wafer-space/chip-on-board-wire-bonded-pcbs/images/prototype1/20251208_205731.jpg

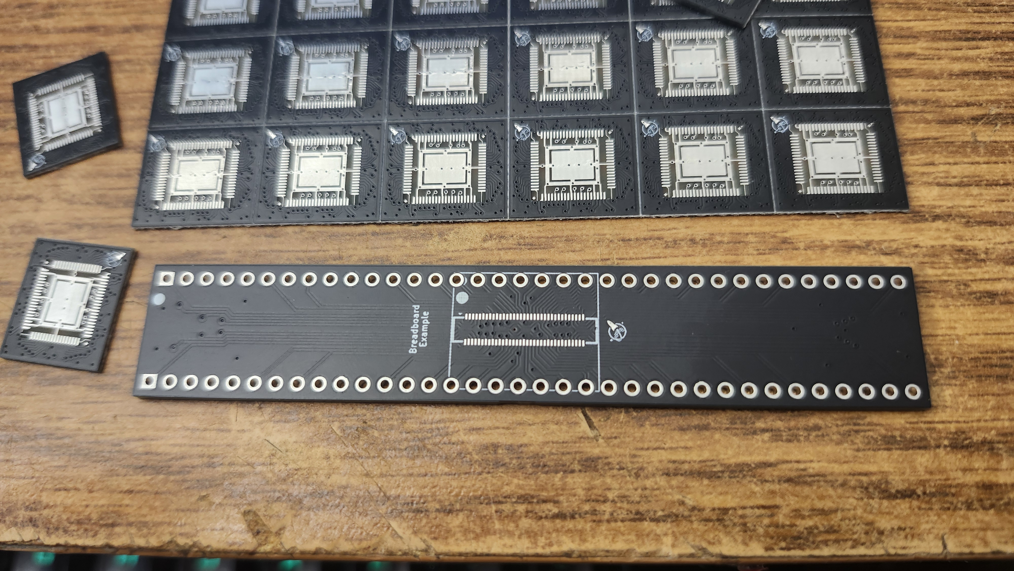
images/prototype1/20251208_205731.jpg
