wafer-space/chip-on-board-wire-bonded-pcbs/images/prototype1/20251208_205753.jpg

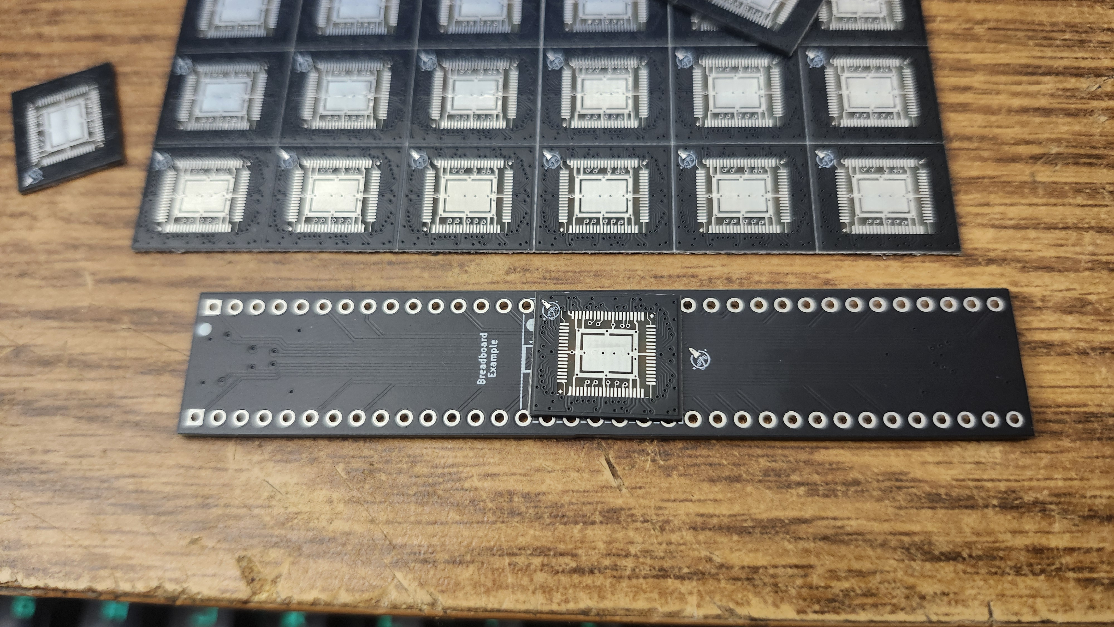
images/prototype1/20251208_205753.jpg
