wafer-space/chip-on-board-wire-bonded-pcbs/images/prototype1/20251208_210338.jpg

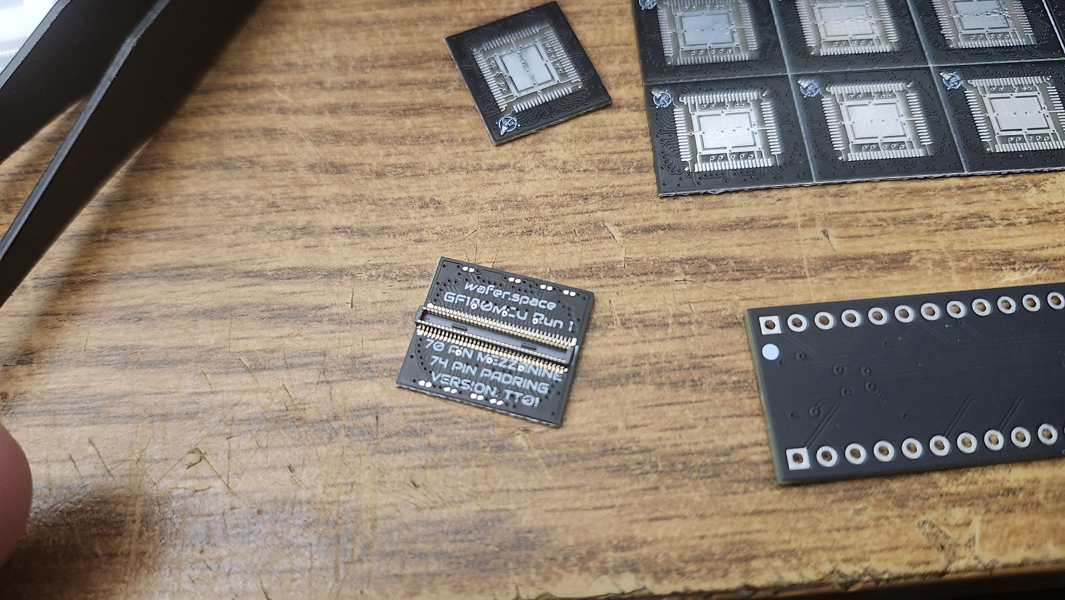
images/prototype1/20251208_210338.jpg
