wafer-space/chip-on-board-wire-bonded-pcbs/images/prototype1/20251208_210347.jpg

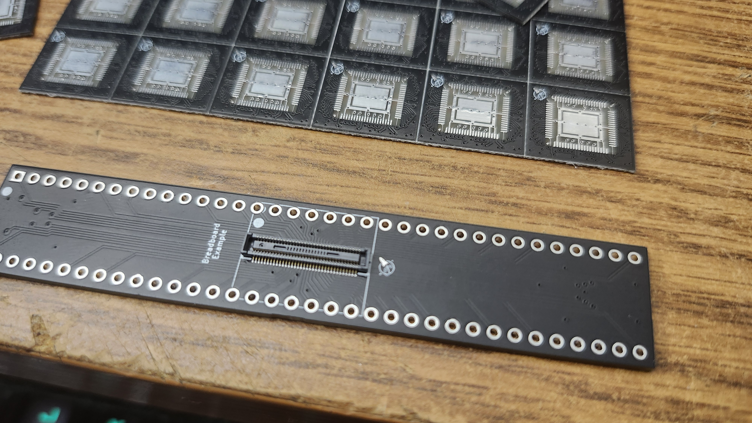
images/prototype1/20251208_210347.jpg
