wafer-space/chip-on-board-wire-bonded-pcbs/images/prototype1/20251217_000424.jpg

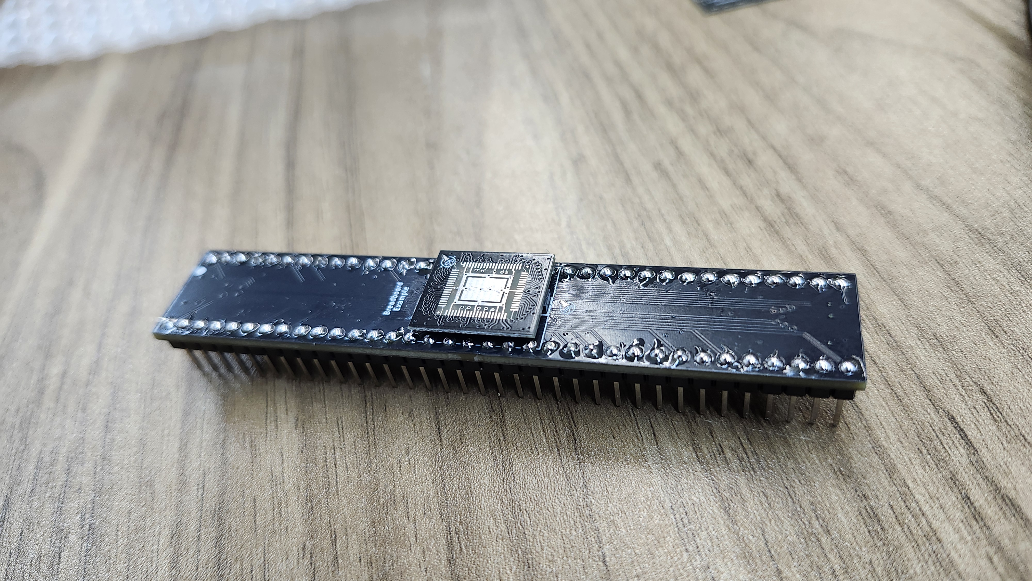
images/prototype1/20251217_000424.jpg
