wafer-space/chip-on-board-wire-bonded-pcbs/images/prototype1/20251217_001013.jpg

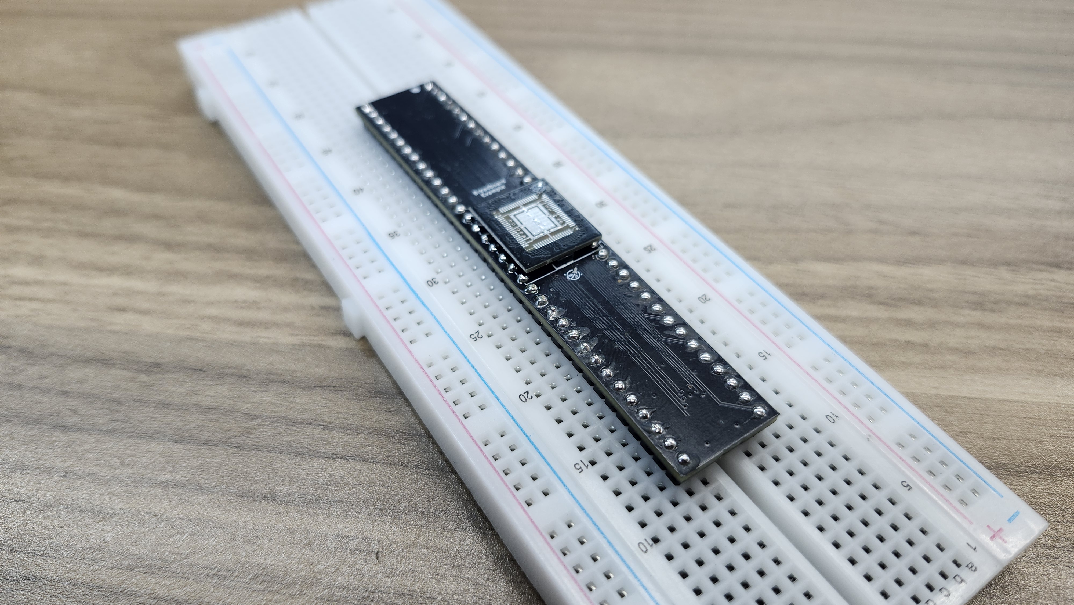
images/prototype1/20251217_001013.jpg
