wafer-space/chip-on-board-wire-bonded-pcbs/images/prototype1/20251217_001034.jpg

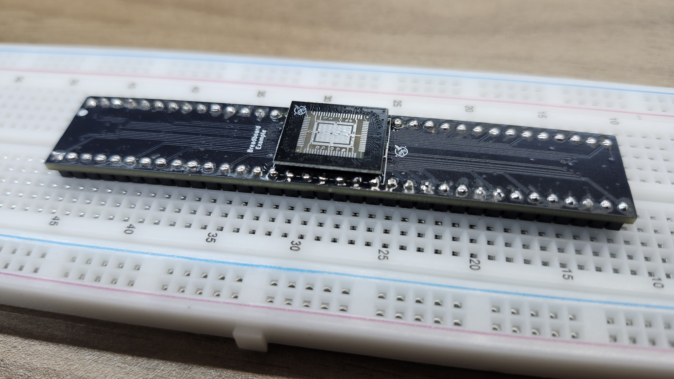
images/prototype1/20251217_001034.jpg
