wafer-space/chip-on-board-wire-bonded-pcbs/images/prototype1/20251217_003011.jpg

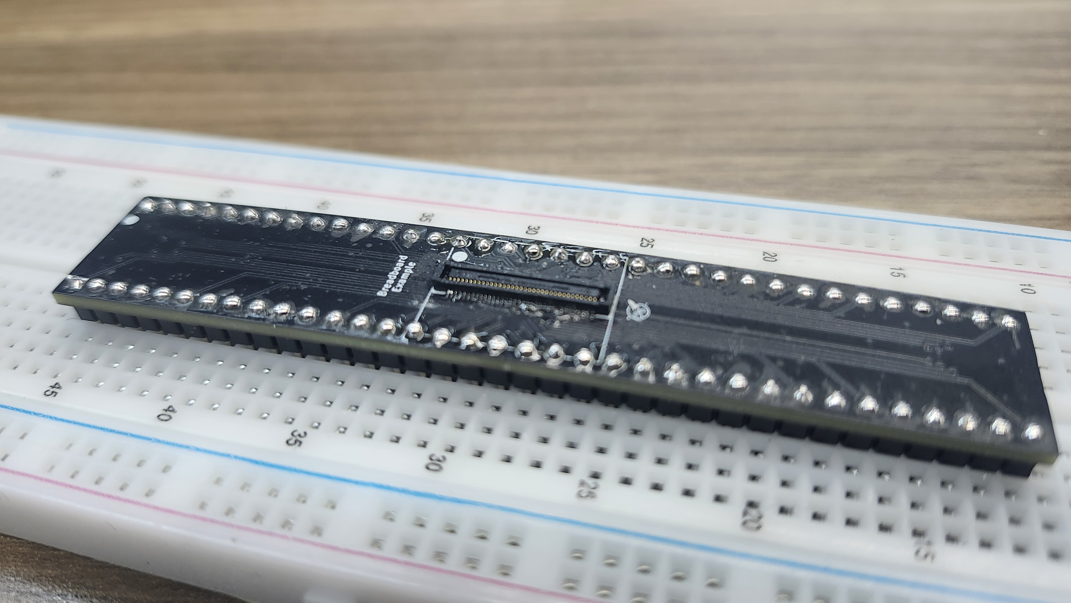
images/prototype1/20251217_003011.jpg
