wafer-space/chip-on-board-wire-bonded-pcbs/run-1/1x0p5-cob/wirebonding/ocd2.png

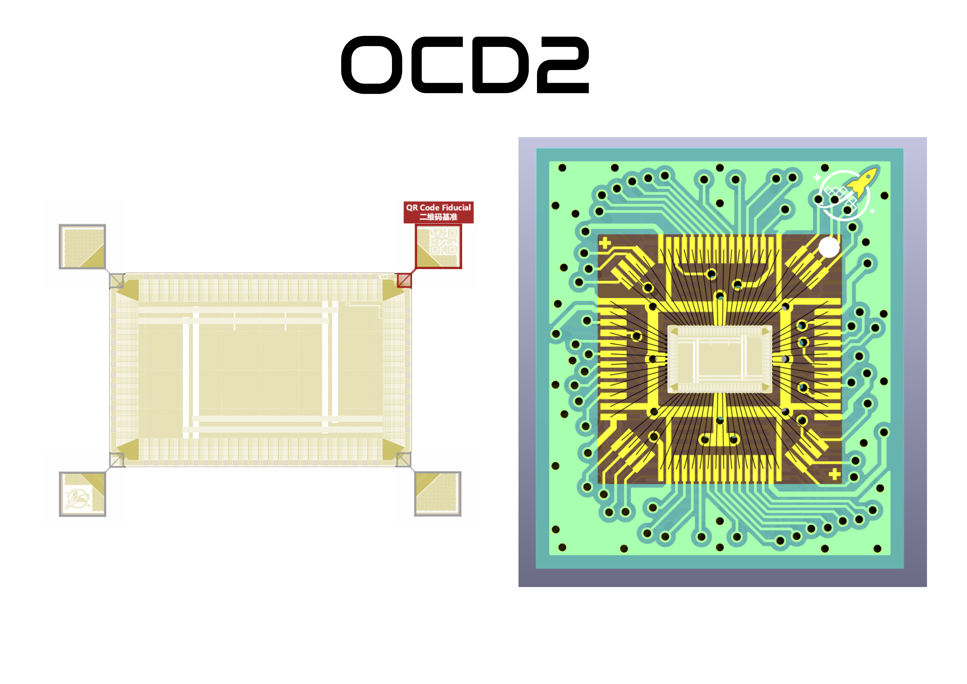
run-1/1x0p5-cob/wirebonding/ocd2.png
