wafer-space/chip-on-board-wire-bonded-pcbs/scratch/mezzanine/mezzanine/mezzanine.png

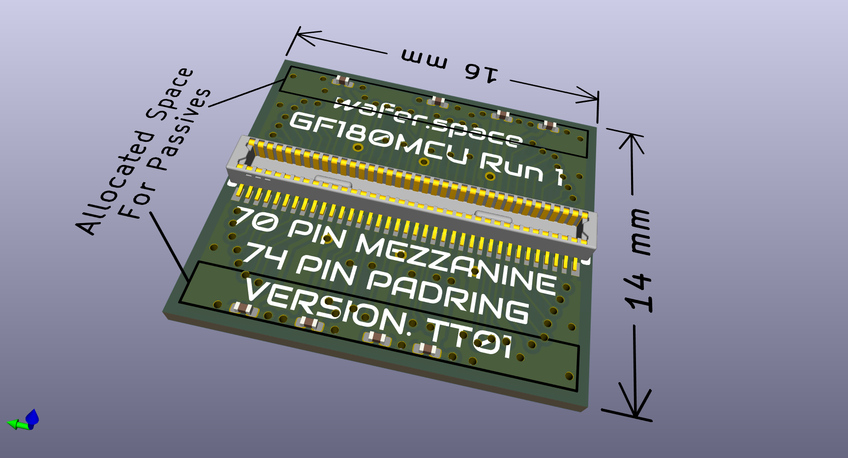
scratch/mezzanine/mezzanine/mezzanine.png
