wafer-space/chip-on-board-wire-bonded-pcbs/run-1/wirebonding/TTPG.pdf

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

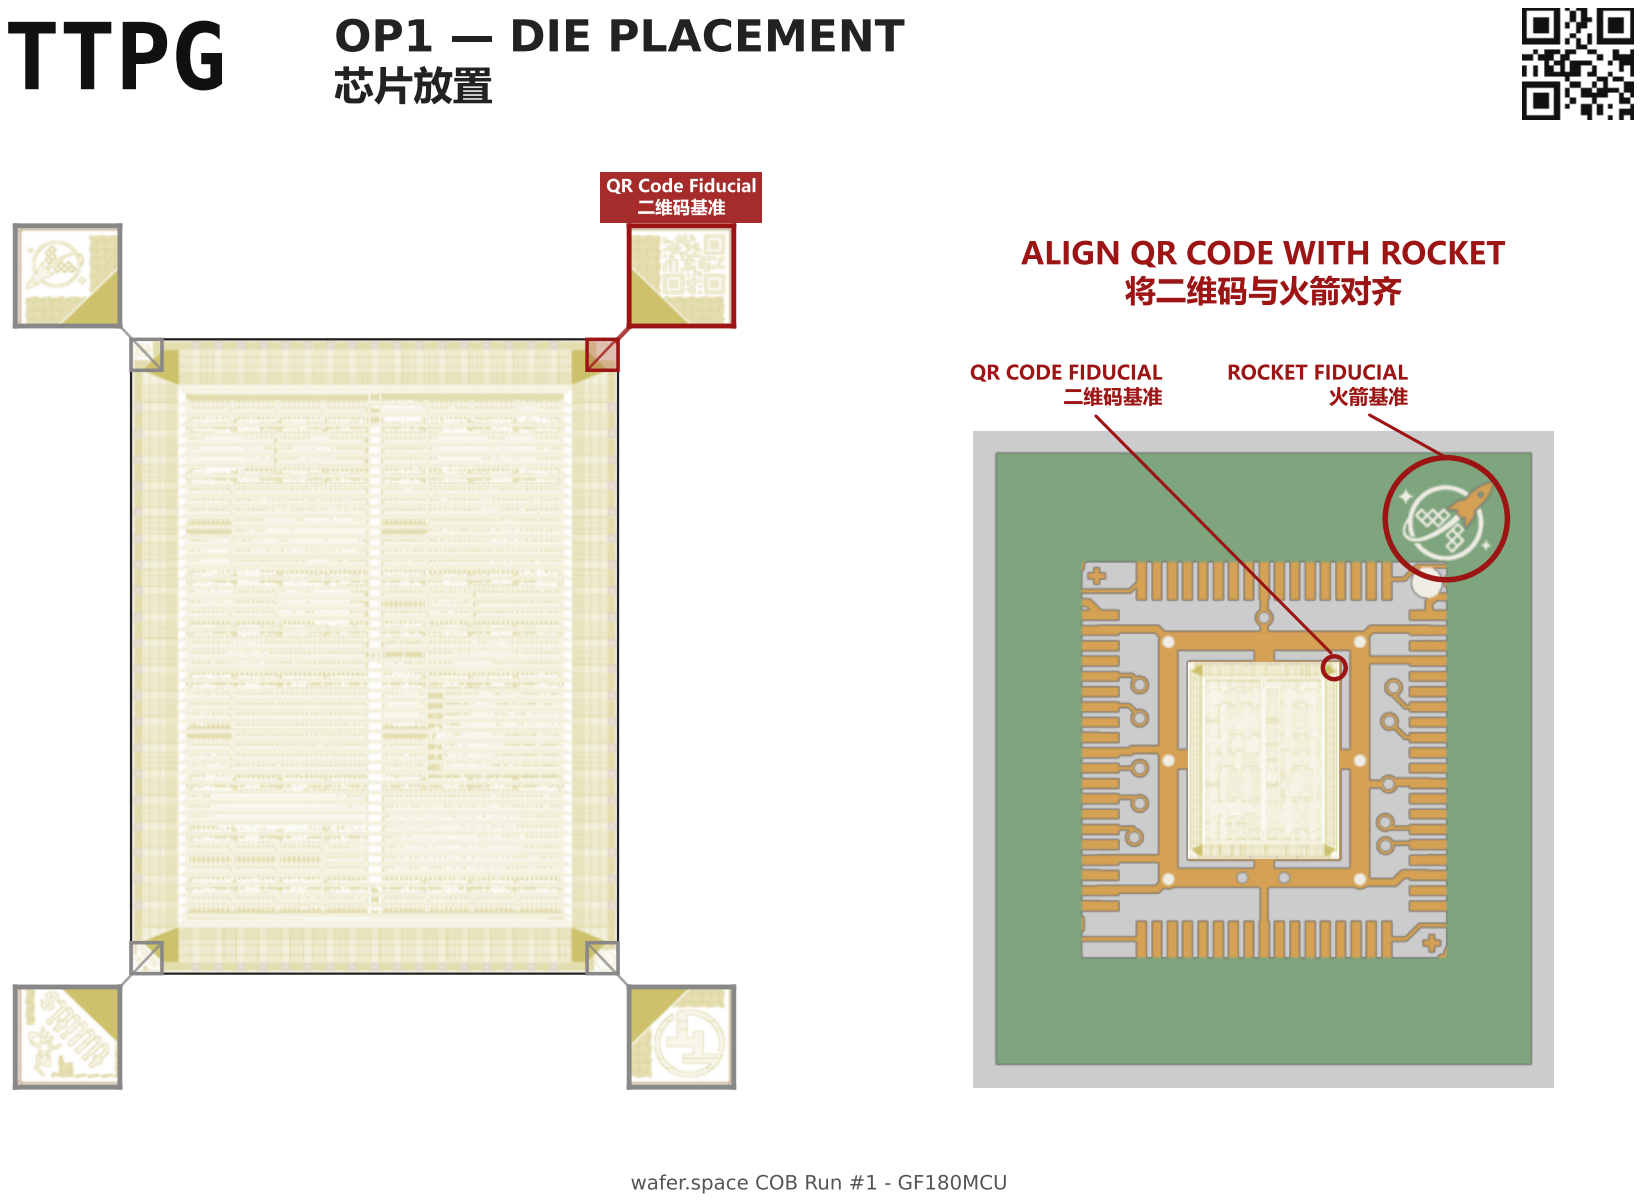
[picture p83: page 1]

# TTPG OP2 WIREBONDING

N

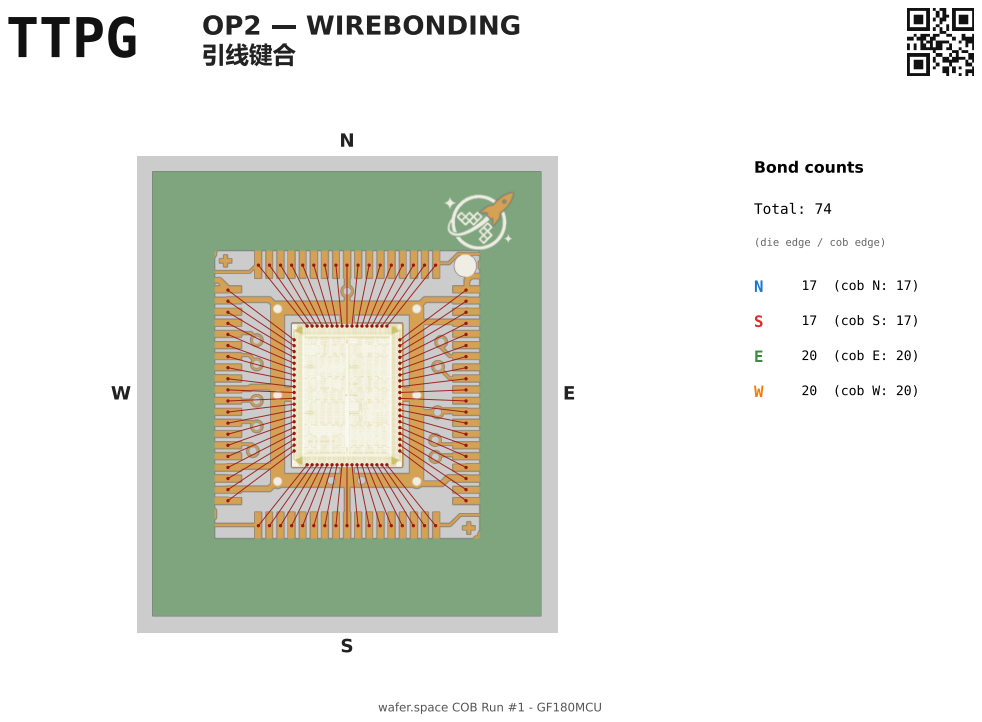
[picture p84: page 2]
Bond counts; Total: 74; N 17 (cob N: 17); S 17 (cob S: 17); E 20 (cob E: 20); W 20 (cob W: 20)

(die edge / cob edge)

wafer.space COB Run #1 - GF180MCU
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
