wafer-space/chip-on-board-wire-bonded-pcbs/images/prototype1/0007.JPG

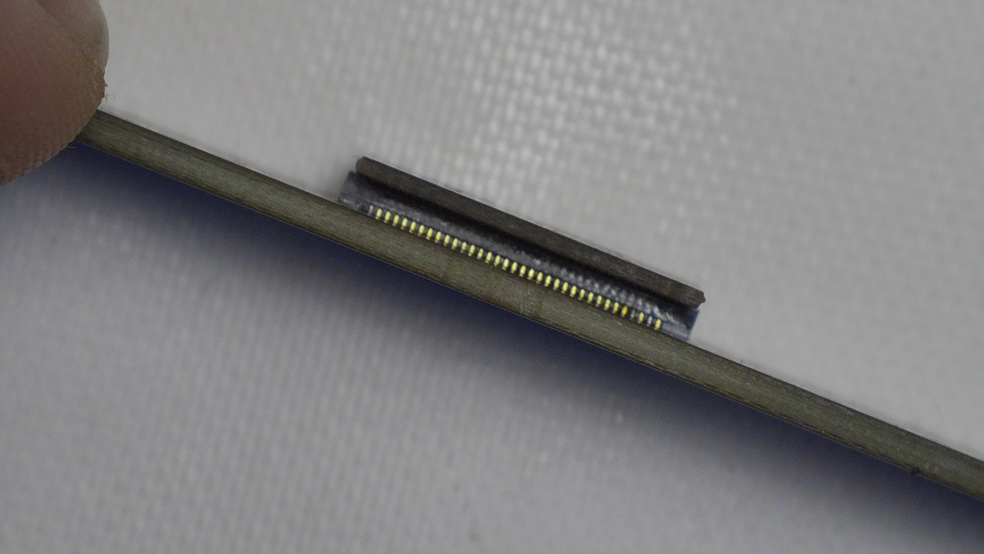
images/prototype1/0007.JPG
