wafer-space/chip-on-board-wire-bonded-pcbs/images/prototype1/mobo_mez.JPG

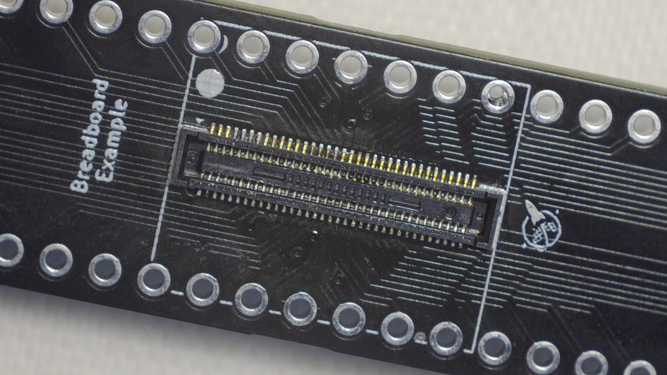
images/prototype1/mobo_mez.JPG
